outdoorbits/case-for-little-backup-box/Raspberry_Pi_zero_2W/Tiny_case/stl/expanded gap/RaspiZero2W_bottom_gap_0.1mm.stl

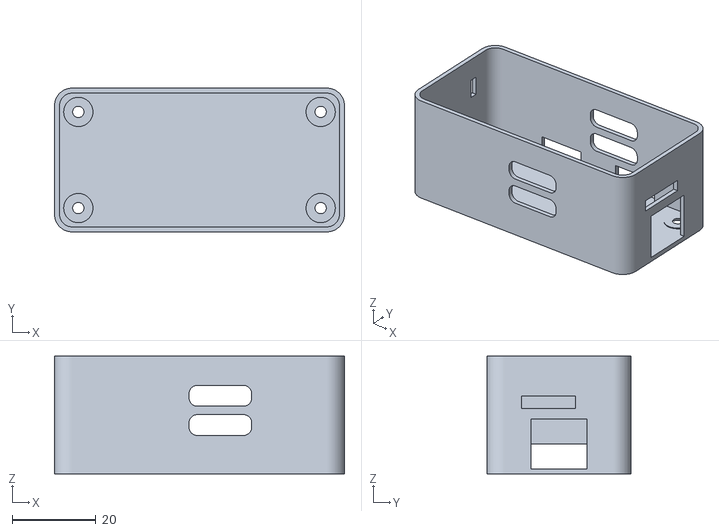
[picture p34: CAD file, 2025-07-05]
Raspberry_Pi_zero_2W/Tiny_case/stl/expanded gap/RaspiZero2W_bottom_gap_0.1mm.stl
69.4 x 34.4 x 28.2
