outdoorbits/case-for-little-backup-box/Raspberry_Pi_zero_2W/Tiny_case/stl/LBB_RaspiZero2W_bottom_zero4u_1.0.stl

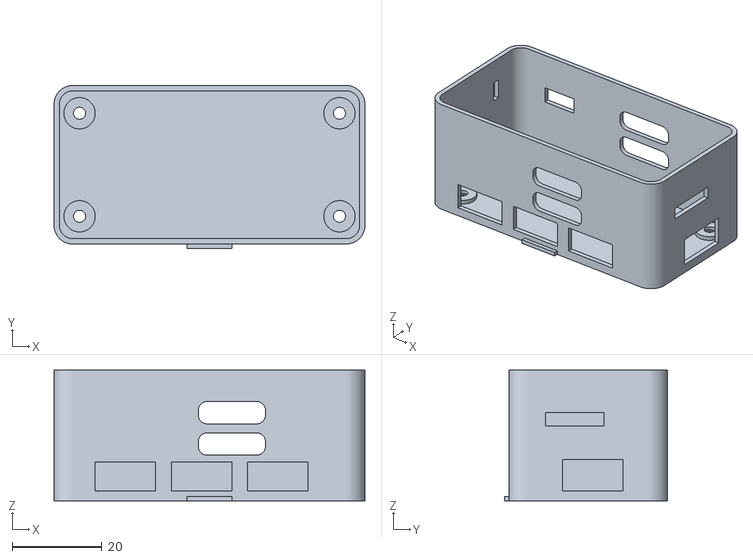
[picture p35: CAD file, 2024-06-05]
Raspberry_Pi_zero_2W/Tiny_case/stl/LBB_RaspiZero2W_bottom_zero4u_1.0.stl
69.4 x 36.4 x 29.2
