outdoorbits/case-for-little-backup-box/Raspberry_Pi_5/lbb-case RPi5.FCStd

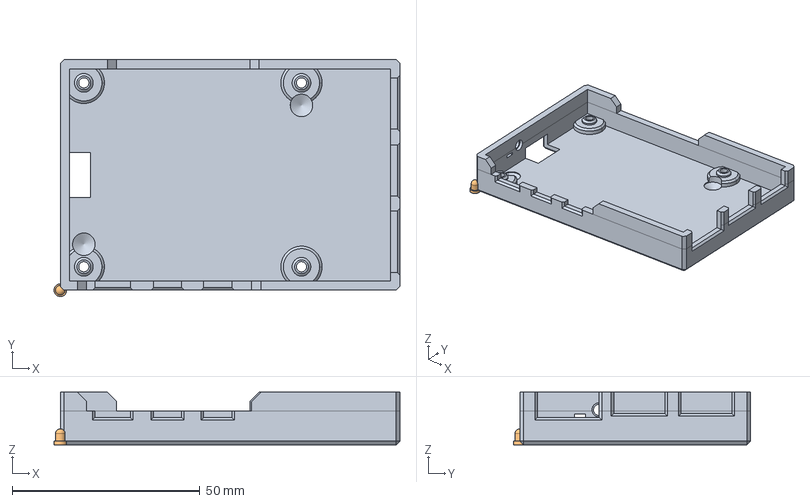
[picture p36: CAD file, 2024-01-30]
Raspberry_Pi_5/lbb-case RPi5.FCStd
92.2 x 63.2 x 14.0 mm
Bottom
power_button
