outdoorbits/case-for-little-backup-box/Raspberry_Pi_5/lbb-case no-buttons RPi5.FCStd

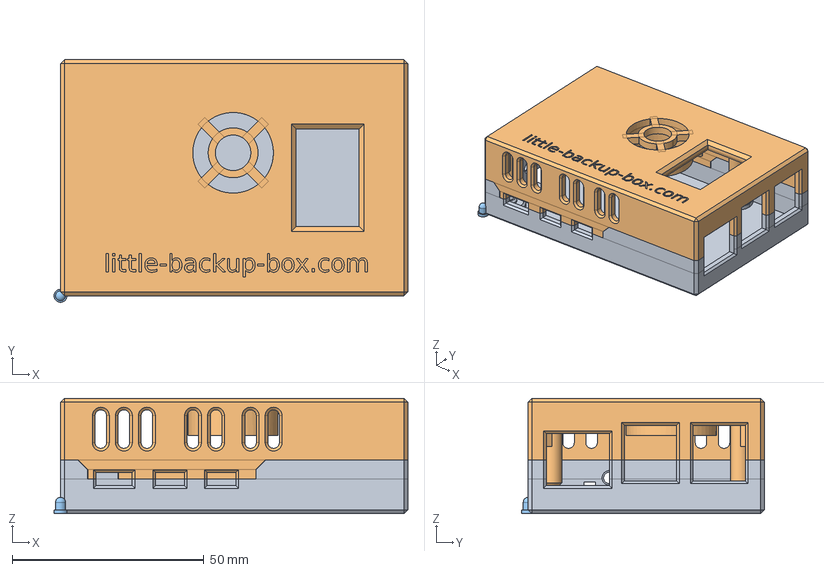
[picture p37: CAD file, 2024-01-30]
Raspberry_Pi_5/lbb-case no-buttons RPi5.FCStd
92.2 x 63.2 x 30.0 mm
Bottom
Top
power_button
