outdoorbits/case-for-little-backup-box/Raspberry_Pi_5/lbb-case RPi5-power_button.stl

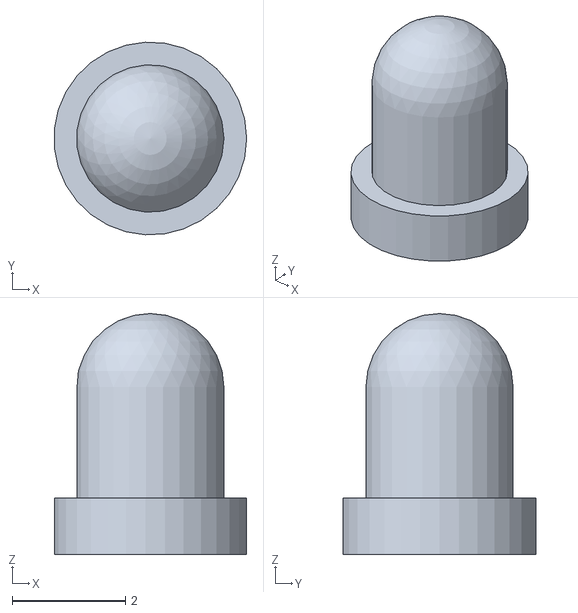
[picture p38: CAD file, 2024-01-30]
Raspberry_Pi_5/lbb-case RPi5-power_button.stl
3.39 x 3.40 x 4.25
